Richard42Graham/WLED-Lion/PCB/pcb-bottom.png

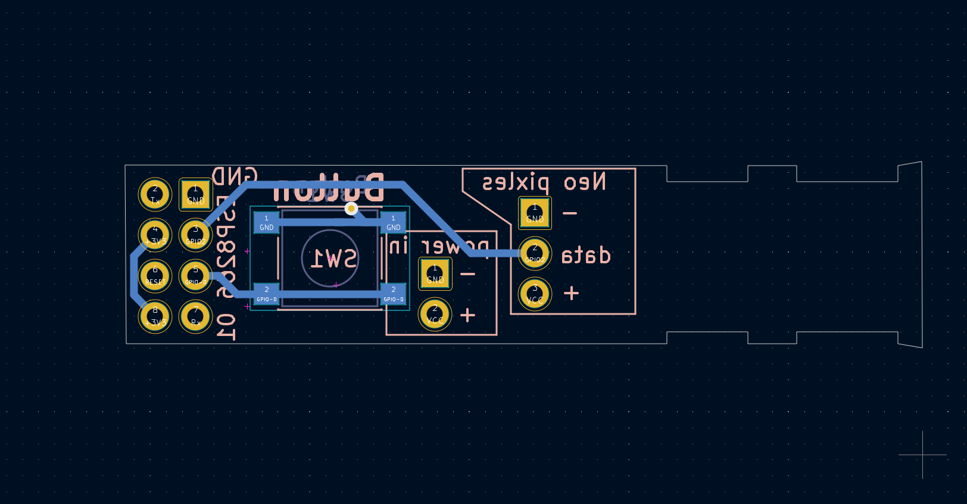
PCB/pcb-bottom.png
