Richard42Graham/WLED-Lion/PCB/PCB-frunt.png

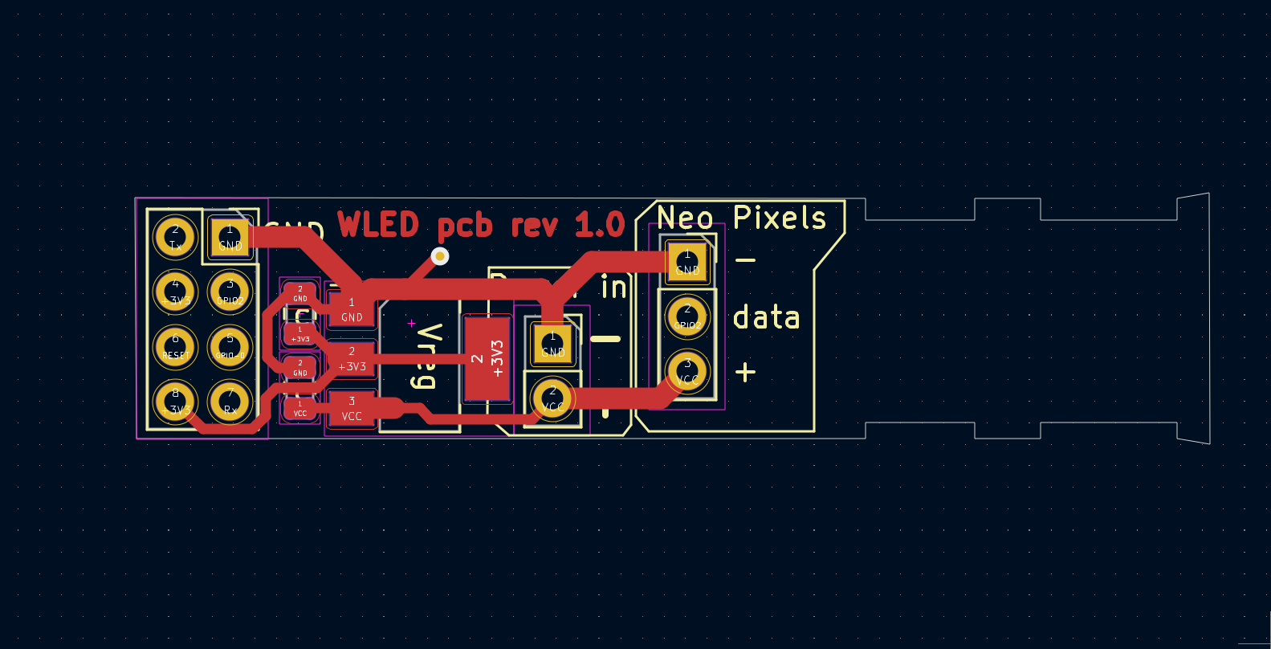
PCB/PCB-frunt.png
